stuthedew/Arduino-Laser-Cat-Turret/Pan_Tilt_laser/stuLaser.cpp

/**************************************************************************/
/*!
    @file     stuLaser.cpp
    @author   Stuart Feichtinger
    @license  MIT (see license.txt)

    Simple library for controlling laser diode
    (https://www.adafruit.com/products/1054) with NPN Transistor (e.g.
    BC547, PN2222 {https://www.adafruit.com/products/756}) as a low-side
    switch.


    @section  HISTORY
    v0.0.1 - First release

*/
/**************************************************************************/


#include "stuLaser.h"

StuLaser::StuLaser(uint8_t pin){
  _pin = pin;

}


void StuLaser::begin( void ){
  pinMode( _pin, OUTPUT ) ;
  digitalWrite( _pin, LOW );
}

void StuLaser::fire( boolean state ){
digitalWrite( _pin, state );

}
